DigitalREP-IL/DR-1-PiRCy/images/20181114_105509.jpg

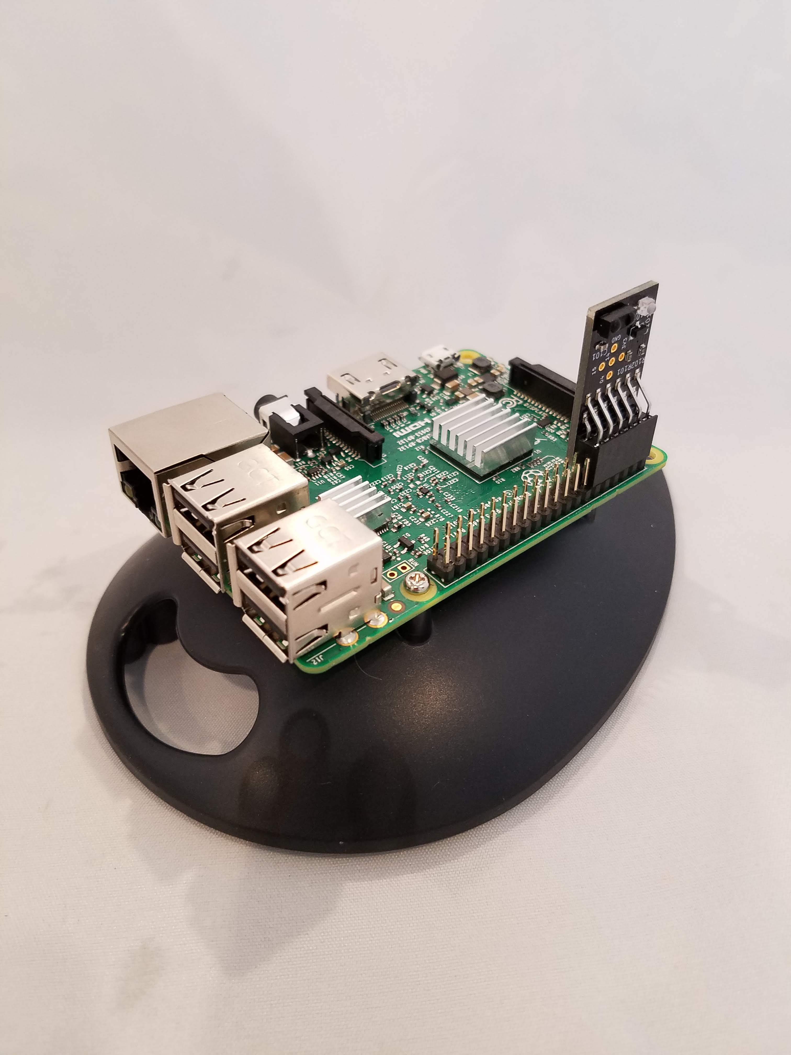
images/20181114_105509.jpg
