DigitalREP-IL/DR-1-PiRCy/images/20181114_105522.jpg

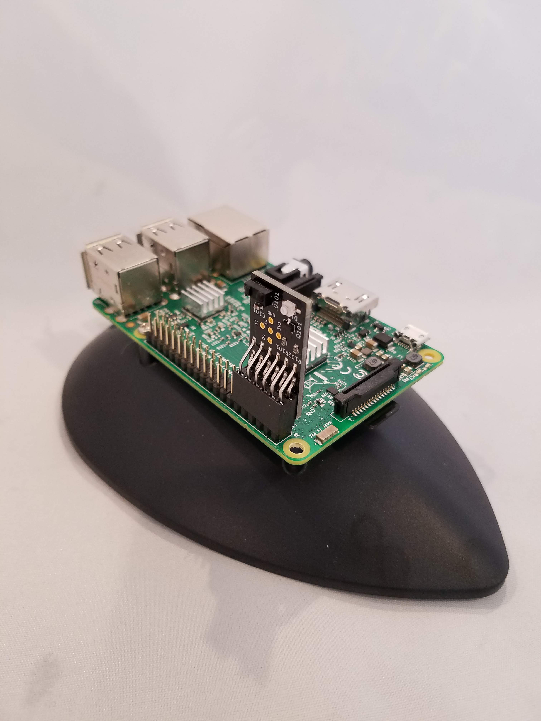
images/20181114_105522.jpg
